haru-ki417/QuakeScope/firmware/QuakeScope/src/app/web_page.h

// 自動生成: tools/embed_web.py（元: firmware/web/index.html、sha256 b72cc43998a17a3e）
// 本体の Web 画面（gzip で圧縮、20469 → 7643 バイト）
#pragma once
#include <Arduino.h>

namespace app {

constexpr size_t kWebPageLen = 7643;
const uint8_t kWebPage[] PROGMEM = {
    0x1f, 0x8b, 0x08, 0x00, 0x00, 0x00, 0x00, 0x00, 0x02, 0x03, 0xad, 0x3c, 0x5b, 0x77, 0xdb, 0x54, 0xba, 0xef, 0xf9, 0x15,
    0xaa, 0xcb, 0x54, 0x16, 0xf1, 0x3d, 0x17, 0x82, 0x1d, 0xa5, 0xc3, 0x75, 0xda, 0x39, 0x05, 0x7a, 0x48, 0x99, 0x9e, 0x39,
    0x59, 0x79, 0x90, 0xad, 0x6d, 0x5b, 0x44, 0x96, 0x8c, 0x24, 0x3b, 0xc9, 0x24, 0x5e, 0x2b, 0x76, 0x28, 0xf4, 0xc6, 0xb4,
    0x14, 0x4a, 0x81, 0x96, 0x53, 0x60, 0x4a, 0x5b, 0x28, 0x6d, 0xe9, 0x94, 0x81, 0x52, 0x0a, 0x7d, 0x38, 0xff, 0x04, 0xd7,
    0x49, 0xfa, 0x34, 0x7f, 0xe1, 0x7c, 0xdf, 0xde, 0x5b, 0xb2, 0x24, 0xcb, 0x49, 0xca, 0x3a, 0x6b, 0x98, 0x78, 0x6b, 0x6b,
    0x5f, 0xbe, 0xfb, 0x6d, 0x6f, 0x75, 0x7a, 0xcf, 0x8b, 0xaf, 0xbd, 0x70, 0xe4, 0xaf, 0x87, 0x5f, 0x12, 0xaa, 0x4e, 0x4d,
    0x9f, 0x19, 0x99, 0xc6, 0x1f, 0x41, 0x57, 0x8c, 0x8a, 0x1c, 0x7b, 0x53, 0x89, 0x61, 0x07, 0x51, 0x54, 0xf8, 0xa9, 0x11,
    0x47, 0x11, 0x4a, 0x55, 0xc5, 0xb2, 0x89, 0x23, 0xc7, 0x1a, 0x4e, 0x39, 0x39, 0x15, 0x73, 0xbb, 0x0d, 0xa5, 0x46, 0xe4,
    0x58, 0x53, 0x23, 0x8b, 0x75, 0xd3, 0x72, 0x62, 0x42, 0xc9, 0x34, 0x1c, 0x62, 0xc0, 0xb0, 0x45, 0x4d, 0x75, 0xaa, 0xb2,
    0x4a, 0x9a, 0x5a, 0x89, 0x24, 0xe9, 0x43, 0x42, 0x33, 0x34, 0x47, 0x53, 0xf4, 0xa4, 0x5d, 0x52, 0x74, 0x22, 0x67, 0x71,
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
    0xc3, 0xce, 0x3f, 0xfb, 0x2c, 0x74, 0x51, 0x91, 0xd2, 0x8c, 0x2a, 0xc8, 0x83, 0x53, 0x28, 0x35, 0x2c, 0x1b, 0x16, 0xa9,
    0x9b, 0x1a, 0x65, 0xe8, 0x62, 0x15, 0xf8, 0x9b, 0xb4, 0xeb, 0x4a, 0x89, 0xc0, 0x1e, 0x8b, 0x96, 0x52, 0xf7, 0x83, 0x92,
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
};

}  // namespace app
