haru-ki417/QuakeScope/core/src/jma_filter_coeffs.h

// 自動生成: tools/fit_jma_digital.py（気象庁の計測震度フィルターを 100 Hz の IIR で近似）
// 近似の誤差: 0.3〜12 Hz で最大 0.55 dB、0.1〜20 Hz で最大 1.13 dB
#pragma once

namespace qs {

constexpr int kJmaSections = 5;
// 各行: b0, b1, b2, a1, a2（a0 = 1）
constexpr double kJmaSos[kJmaSections][5] = {
    {0.087551201474897034, -0.087551201474897034, 0, -0.961957163036533, 0},
    {0.99750796386813068, -1.9950159277362614, 0.99750796386813068, -1.9950110052236689, 0.99502085024885378},
    {0.29489248888383851, 0.58978497776767702, 0.29489248888383851, 0.42532756922889814, -0.24575761369354412},
    {0.29472701611132296, 0.58945403222264592, 0.29472701611132296, 0.4248544327488562, -0.2459463683035642},
    {1.9969330449719629, -1.3617321371117395, -0.25157325432217814, -1.5456256855107195, 0.56146624225080477},
};

constexpr double kJmaSampleRate = 100.0;

}  // namespace qs
